miu-lab/midi_controller_2.0/src/app/MidiControllerApp.cpp

#include "MidiControllerApp.hpp"

#include "app/di/DependencyContainer.hpp"

#include "core/TaskScheduler.hpp"
#include "core/domain/interfaces/IConfiguration.hpp"
#include "core/domain/interfaces/IInputSystem.hpp"
#include "core/domain/interfaces/IMidiSystem.hpp"
#include "core/domain/interfaces/IUISystem.hpp"
#include "core/utils/Error.hpp"


MidiControllerApp::MidiControllerApp(std::shared_ptr<DependencyContainer> container)
    : m_container(container) {
    m_scheduler = m_container->resolve<TaskScheduler>();
}

MidiControllerApp::~MidiControllerApp() {
}

Result<bool> MidiControllerApp::init() {
    // 1. Obtention des références aux sous-systèmes
    m_configSystem = m_container->resolve<IConfiguration>();
    m_inputSystem = m_container->resolve<IInputSystem>();
    m_midiSystem = m_container->resolve<IMidiSystem>();
    m_uiSystem = m_container->resolve<IUISystem>();

    if (!m_configSystem || !m_inputSystem || !m_midiSystem || !m_uiSystem) {
        return Result<bool>::error({ErrorCode::DependencyMissing, "Sous-systèmes manquants"});
    }
    
    // Le décorateur MIDI pour les événements est maintenant créé et géré par MidiSubsystem

    return Result<bool>::success(true);
}

void MidiControllerApp::update() {
    // Mettre à jour le scheduler de tâches en premier
    if (m_scheduler) {
        m_scheduler->update();
    }
}
