miu-lab/midi_controller_2.0/src/app/MidiControllerApp.hpp

#pragma once

#include <memory>

#include "core/utils/Result.hpp"
#include "core/TaskScheduler.hpp"

// Déclarations anticipées
class DependencyContainer;
class IConfiguration;
class IInputSystem;
class IMidiSystem;
class IUISystem;

/**
 * @brief Application principale du contrôleur MIDI
 */
class MidiControllerApp {
public:
    explicit MidiControllerApp(std::shared_ptr<DependencyContainer> container);
    ~MidiControllerApp();

    // Méthodes principales
    Result<bool> init();
    void update();

private:
    // Conteneur de dépendances
    std::shared_ptr<DependencyContainer> m_container;

    // Sous-systèmes
    std::shared_ptr<IConfiguration> m_configSystem;
    std::shared_ptr<IInputSystem> m_inputSystem;
    std::shared_ptr<IMidiSystem> m_midiSystem;
    std::shared_ptr<IUISystem> m_uiSystem;
    
    std::shared_ptr<TaskScheduler> m_scheduler;
    
    
};
