miu-lab/midi_controller_2.0/src/adapters/secondary/hardware/input/encoders/EncoderManager.hpp

// adapters/secondary/hardware/input/encoders/EncoderManager.hpp
#pragma once
#include <memory>
#include <vector>

#include "adapters/secondary/hardware/input/encoders/EncoderConfig.hpp"
#include "adapters/secondary/hardware/input/encoders/QuadratureEncoder.hpp"
#include "core/ports/input/EncoderPort.hpp"

/**
 * @brief Construit et expose tous les EncoderPort* à partir de configs.
 */
class EncoderManager {
public:
    explicit EncoderManager(const std::vector<EncoderConfig>& cfgs);

    void updateAll();
    const std::vector<EncoderPort*>& getEncoders() const;

private:
    std::vector<std::unique_ptr<EncoderPort>> ownedEncoders_;
    std::vector<EncoderPort*> encoders_;
};
