miu-lab/midi_controller_2.0/src/core/use_cases/ButtonStateProcessor.hpp

#pragma once

#include <functional>
#include <vector>

/**
 * @brief Template pour traiter les changements d'état de boutons
 * 
 * Factorisation de la logique commune entre boutons normaux et boutons d'encodeurs.
 * Évite la duplication de code tout en gardant les performances optimales.
 */
template<typename Port>
void processButtonChanges(const std::vector<Port*>& ports, 
                         std::vector<bool>& lastStates,
                         std::function<void(uint16_t, bool)> callback) {
    for (size_t i = 0; i < ports.size(); ++i) {
        bool pressed = ports[i]->isPressed();
        if (pressed != lastStates[i]) {
            lastStates[i] = pressed;
            uint16_t buttonId = ports[i]->getId();
            callback(buttonId, pressed);
        }
    }
}
