miu-lab/midi_controller_2.0/src/adapters/secondary/midi/MidiMapper.cpp

#include "adapters/secondary/midi/MidiMapper.hpp"

#include <stdarg.h>

#include "config/SystemConstants.hpp"

#include "config/GlobalSettings.hpp"
  // Pour avoir accès à PERFORMANCE_MODE
#include "core/domain/events/core/EventTypes.hpp"
#include "tools/Diagnostics.hpp"

//=============================================================================
// Construction et initialisation
//=============================================================================

MidiMapper::MidiMapper(MidiOutputPort& midiOut, CommandManager& commandManager)
    : midiOut_(midiOut),
      commandManager_(commandManager),
      defaultConfig_(
          {0, 0, false})  // Canal 0, CC 0, mode absolu
{
    // Initialisation préalable des pool d'objets
    for (auto& cmd : midiCCCommandPool_) {
        cmd.reset(midiOut_, 0, 0, 0, 0);
    }

    for (auto& cmd : midiNoteCommandPool_) {
        cmd.reset(midiOut_, 0, 0, 0, 0);
    }
}

//=============================================================================
// Implémentation des méthodes utilitaires
//=============================================================================

uint32_t MidiMapper::makeCompositeKey(InputId controlId, MappingControlType type) {
    return static_cast<uint32_t>(controlId) << 8 | static_cast<uint8_t>(type);
}

SendMidiCCCommand& MidiMapper::getNextCCCommand() {
    SendMidiCCCommand& cmd = midiCCCommandPool_[nextCCCommandIndex_];
    nextCCCommandIndex_ = (nextCCCommandIndex_ + 1) % COMMAND_POOL_SIZE;
    return cmd;
}

SendMidiNoteCommand& MidiMapper::getNextNoteCommand() {
    SendMidiNoteCommand& cmd = midiNoteCommandPool_[nextNoteCommandIndex_];
    nextNoteCommandIndex_ = (nextNoteCommandIndex_ + 1) % COMMAND_POOL_SIZE;
    return cmd;
}

void MidiMapper::logDiagnostic(const char* format, ...) const {
#ifndef PERFORMANCE_MODE
    char buffer[100];
    va_list args;
    va_start(args, format);
    vsnprintf(buffer, sizeof(buffer), format, args);
    va_end(args);
    DIAG_ON_EVENT(buffer);
#endif
}


//=============================================================================
// Gestion des mappings
//=============================================================================

void MidiMapper::setMappingFromControlDefinition(const ControlDefinition& controlDef) {
    // Traiter le premier mapping MIDI trouvé dans la définition de contrôle
    for (const auto& mappingSpec : controlDef.mappings) {
        if (mappingSpec.role == MappingRole::MIDI) {
            // Extraire la configuration MIDI
            const auto& midiConfig = std::get<ControlDefinition::MidiConfig>(mappingSpec.config);
            
            // Créer une nouvelle info de mapping simplifiée
            MappingInfo info;
            info.midiConfig = midiConfig;
            info.lastMidiValue = 0;
            info.lastEncoderPosition = 0;  // Sera initialisé lors du premier appel
            info.isFirstCall = true;

            // Créer une clé composite qui inclut le type de contrôle
            uint32_t compositeKey = makeCompositeKey(controlDef.id, mappingSpec.appliesTo);

            // Supprimer l'ancien mapping s'il existe
            auto it = mappings_.find(compositeKey);
            if (it != mappings_.end()) {
                mappings_.erase(it);
            }

            // Ajouter le nouveau mapping
            mappings_[compositeKey] = std::move(info);

            // TODO DEBUG MSG

                          
            // Traiter seulement le premier mapping MIDI pour cette version
            break;
        }
    }
}

bool MidiMapper::removeMapping(InputId controlId) {
    // Nous devons vérifier tous les types de contrôle possibles
    bool removed = false;

    // Essayer de supprimer le mapping pour l'encodeur
    uint32_t encoderKey = makeCompositeKey(controlId, MappingControlType::ENCODER);
    auto encoderIt = mappings_.find(encoderKey);
    if (encoderIt != mappings_.end()) {
        mappings_.erase(encoderIt);
        removed = true;
    }

    // Essayer de supprimer le mapping pour le bouton d'encodeur
    uint32_t buttonKey = makeCompositeKey(controlId, MappingControlType::BUTTON);
    auto buttonIt = mappings_.find(buttonKey);
    if (buttonIt != mappings_.end()) {
        mappings_.erase(buttonIt);
        removed = true;
    }

    if (removed) {
        logDiagnostic("Mapping supprimé: ID=%d", controlId);
    }

    return removed;
}

bool MidiMapper::hasMapping(InputId controlId) const {
    // Vérifier tous les types de contrôle possibles
    uint32_t encoderKey = makeCompositeKey(controlId, MappingControlType::ENCODER);
    if (mappings_.find(encoderKey) != mappings_.end()) {
        return true;
    }

    uint32_t buttonKey = makeCompositeKey(controlId, MappingControlType::BUTTON);
    if (mappings_.find(buttonKey) != mappings_.end()) {
        return true;
    }

    return false;
}

ControlDefinition::MidiConfig MidiMapper::getMidiConfig(InputId controlId) const {
    // Vérifier pour encoder en premier
    uint32_t encoderKey = makeCompositeKey(controlId, MappingControlType::ENCODER);
    auto encoderIt = mappings_.find(encoderKey);
    if (encoderIt != mappings_.end()) {
        return encoderIt->second.midiConfig;
    }

    // Puis vérifier pour bouton d'encodeur
    uint32_t buttonKey = makeCompositeKey(controlId, MappingControlType::BUTTON);
    auto buttonIt = mappings_.find(buttonKey);
    if (buttonIt != mappings_.end()) {
        return buttonIt->second.midiConfig;
    }

    return defaultConfig_;
}


//=============================================================================
// Méthodes de traitement des encodeurs
//=============================================================================

bool MidiMapper::shouldProcessEncoder(EncoderId encoderId, int32_t position) {
    // TODO: Implémenter la limitation de taux et la détection de doublons
    // Pour l'instant, tous les événements sont traités
    return true;
}

int32_t MidiMapper::applyEncoderSensitivity(int32_t delta, EncoderId encoderId) {
    // Appliquer le facteur de sensibilité global
    float sensitivity = GlobalSettings::getInstance().getEncoderSensitivity();

    logDiagnostic("Pre-sensibilité: Enc=%d Delta=%ld", encoderId, delta);

    if (sensitivity != 1.0f) {
        // Appliquer la sensibilité tout en préservant le signe
        int32_t delta_sign = (delta > 0) ? 1 : -1;
        int32_t delta_abs = abs(delta);

        // Appliquer la sensibilité et assurer qu'un mouvement réel produit au moins 1 delta
        int32_t scaled_delta_abs = static_cast<int32_t>(delta_abs * sensitivity);
        if (scaled_delta_abs == 0 && delta_abs > 0) scaled_delta_abs = 1;

        // Reconstruire delta avec son signe
        int32_t new_delta = delta_sign * scaled_delta_abs;

        logDiagnostic("Post-sensibilité: Enc=%d Delta=%ld->%ld Sens=%.2f",
                      encoderId,
                      delta,
                      new_delta,
                      sensitivity);

        return new_delta;
    }

    return delta;
}

int16_t MidiMapper::calculateMidiValue(MappingInfo& info, int32_t delta, int32_t position) {
    const ControlDefinition::MidiConfig& midiConfig = info.midiConfig;
    
    uint8_t newValue;
    
    if (midiConfig.isRelative) {
        // Mode relatif : ajouter le delta à la dernière valeur
        int16_t temp = info.lastMidiValue + delta;
        newValue = constrain(temp, 0, 127);
    } else {
        // Mode absolu avec OFFSET : décaler la position pour que le centre soit 64
        // Plage encodeur typique : -127 à +127 -> MIDI 0 à 127
        int32_t offsetPosition = position + 64;  // Décaler de 64 pour centrer
        newValue = constrain(offsetPosition, 0, 127);
    }

    return newValue;
}

void MidiMapper::processEncoderChange(EncoderId encoderId, int32_t position) {
    // MidiMapper est responsable de tout le traitement des encodeurs MIDI,
    // y compris la limitation de taux, le suivi des positions et la détection des doublons.


    // Vérifier si l'encodeur doit être traité (limitation de taux)
    if (!shouldProcessEncoder(encoderId, position)) {
        return;
    }

    // Rechercher le mapping avec l'ID de l'encodeur et le type ENCODER_ROTATION
    uint32_t encoderKey = makeCompositeKey(encoderId, MappingControlType::ENCODER);
    auto it = mappings_.find(encoderKey);
    if (it == mappings_.end()) {
        return;  // Pas de mapping pour cet encodeur
    }

    auto& [key, mappingInfo] = *it;
    const ControlDefinition::MidiConfig& midiConfig = mappingInfo.midiConfig;

    // Si c'est le premier appel, initialiser avec la position actuelle
    if (mappingInfo.isFirstCall) {
        mappingInfo.lastEncoderPosition = position;
        mappingInfo.isFirstCall = false;
        return;  // Pas de changement lors de l'initialisation
    }

    // Calculer le delta de mouvement
    int32_t delta = position - mappingInfo.lastEncoderPosition;
    if (delta == 0) {
        return;  // Pas de changement
    }

    // Appliquer la sensibilité aux mouvements d'encodeur
    delta = applyEncoderSensitivity(delta, encoderId);

    // Mettre à jour la dernière position
    mappingInfo.lastEncoderPosition = position;

    // Calculer la nouvelle valeur MIDI selon le mode
    int16_t newValue = calculateMidiValue(mappingInfo, delta, position);

    // Ne rien faire si la valeur n'a pas changé
    if (newValue == mappingInfo.lastMidiValue) {
        return;
    }


    // Mettre à jour et envoyer la nouvelle valeur
    mappingInfo.lastMidiValue = static_cast<uint8_t>(newValue);

    // Utiliser le pool de commandes
    SendMidiCCCommand& command = getNextCCCommand();
    command.reset(midiOut_,
                  midiConfig.channel,
                  midiConfig.control,
                  static_cast<uint8_t>(newValue),
                  encoderId);
    commandManager_.executeShared(command);
}

//=============================================================================
// Méthodes de traitement des boutons
//=============================================================================

void MidiMapper::processButtonEvent(InputId buttonId, bool pressed, MappingControlType type) {

    // Créer une clé composite à partir de l'ID et du type
    uint32_t buttonKey = makeCompositeKey(buttonId, type);

    auto it = mappings_.find(buttonKey);
    if (it == mappings_.end()) {
        return;  // Pas de mapping pour ce bouton
    }

    MappingInfo& info = it->second;
    const ControlDefinition::MidiConfig& midiConfig = info.midiConfig;

    // Pour les boutons, on utilise des notes MIDI au lieu de CC
    uint8_t velocity = pressed ? 127 : 0;

    // Utiliser le pool d'objets pour créer la commande
    SendMidiNoteCommand& command = getNextNoteCommand();
    command.reset(midiOut_, midiConfig.channel, midiConfig.control, velocity);

    // Si c'est une note on, la stocker pour pouvoir la couper plus tard
    if (pressed) {
        // Pour les notes actives, nous gardons toujours des objets gérés par smart pointers
        // car elles doivent persister longtemps
        auto noteCmd = std::make_unique<SendMidiNoteCommand>(midiOut_,
                                                             midiConfig.channel,
                                                             midiConfig.control,
                                                             velocity);
        activeNotes_[buttonId] = std::move(noteCmd);
        activeNotes_[buttonId]->execute();
    } else {
        // Si c'est une note off, utiliser la commande et la supprimer
        auto noteIt = activeNotes_.find(buttonId);
        if (noteIt != activeNotes_.end()) {
            noteIt->second->undo();  // Undo = Note Off
            activeNotes_.erase(noteIt);
        } else {
            // Si pas de note active, simplement exécuter la commande du pool
            commandManager_.executeShared(command);
        }
    }
}


void MidiMapper::processButtonPress(ButtonId buttonId, bool pressed) {
    processButtonEvent(buttonId, pressed, MappingControlType::BUTTON);
}

//=============================================================================
// Méthodes de maintenance et mises à jour
//=============================================================================

void MidiMapper::update() {
    // Mettre à jour les commandes de notes actives
    for (auto& pair : activeNotes_) {
        pair.second->update();
    }

    // Supprimer les notes qui ne sont plus actives
    for (auto it = activeNotes_.begin(); it != activeNotes_.end();) {
        if (!it->second->isNoteActive()) {
            logDiagnostic("Note supprimée: ID=%d", it->first);
            it = activeNotes_.erase(it);
        } else {
            ++it;
        }
    }
}

//=============================================================================
// Gestion des événements
//=============================================================================

bool MidiMapper::onEvent(const Event& event) {
    // Traiter les différents types d'événements
    switch (event.getType()) {
    case EventTypes::HighPriorityEncoderChanged: {
        const HighPriorityEncoderChangedEvent& encEvent =
            static_cast<const HighPriorityEncoderChangedEvent&>(event);
        processEncoderChange(encEvent.encoderId, encEvent.position);
        return true;
    }


    case EventTypes::HighPriorityButtonPress: {
        const HighPriorityButtonPressEvent& buttonEvent =
            static_cast<const HighPriorityButtonPressEvent&>(event);
        // TODO DEBUG MSG
        processButtonPress(buttonEvent.buttonId, buttonEvent.pressed);
        return true;
    }

    // Gérer aussi les types standard d'événements pour la compatibilité
    case EventTypes::EncoderTurned: {
        const EncoderTurnedEvent& encEvent = static_cast<const EncoderTurnedEvent&>(event);
        processEncoderChange(encEvent.id, encEvent.position);
        return true;
    }

    case EventTypes::EncoderButton: {
        const EncoderButtonEvent& buttonEvent = static_cast<const EncoderButtonEvent&>(event);
        processButtonPress(buttonEvent.id, buttonEvent.pressed);
        return true;
    }

    case EventTypes::ButtonPressed: {
        const ButtonPressedEvent& buttonEvent = static_cast<const ButtonPressedEvent&>(event);
        processButtonPress(buttonEvent.id, true);
        return true;
    }

    case EventTypes::ButtonReleased: {
        const ButtonReleasedEvent& buttonEvent = static_cast<const ButtonReleasedEvent&>(event);
        processButtonPress(buttonEvent.id, false);
        return true;
    }
    }

    return false;  // Evénement non traité
}
