miu-lab/midi_controller_2.0/src/app/services/InputSystem.cpp

#include "app/services/InputSystem.hpp"

#include "app/di/DependencyContainer.hpp"
#include "app/services/NavigationConfigService.hpp"

InputSystem::InputSystem()
    : encoderManager_({}),
      processEncoders_(encoderManager_.getEncoders()),
      buttonManager_({}),
      processButtons_(buttonManager_.getButtons()),
      inputController_(nullptr),
      container_(nullptr),
      usingContainer_(false) {
      
    // Créer un service de navigation par défaut
    auto navConfigService = std::make_shared<NavigationConfigService>();
    
    // Créer InputController
    inputController_ = std::make_shared<InputController>(navConfigService);

    // Configurer les processeurs
    processEncoders_.setInputController(inputController_.get());
    processButtons_.setInputController(inputController_.get());
}

InputSystem::InputSystem(std::shared_ptr<DependencyContainer> container)
    : encoderManager_({}),
      processEncoders_(encoderManager_.getEncoders()),
      buttonManager_({}),
      processButtons_(buttonManager_.getButtons()),
      inputController_(nullptr),
      container_(container),
      usingContainer_(true) {
      
    initializeDependencies();
}

void InputSystem::initializeDependencies() {
#ifndef DISABLE_CONTROLLERS
    // Récupérer NavigationConfigService
    std::shared_ptr<NavigationConfigService> navConfigService;
    
    if (usingContainer_ && container_) {
        // Essayer de récupérer depuis le container
        navConfigService = container_->resolve<NavigationConfigService>();
        
        // Si le service n'est pas dans le container, créer une nouvelle instance
        if (!navConfigService) {
            navConfigService = std::make_shared<NavigationConfigService>();
            container_->registerDependency<NavigationConfigService>(navConfigService);
        }
    } else {
        // Créer un service de navigation par défaut
        navConfigService = std::make_shared<NavigationConfigService>();
    }
    
    // Créer InputController
    inputController_ = std::make_shared<InputController>(navConfigService);

    if (usingContainer_ && container_) {
        // Enregistrer dans le container
        container_->registerDependency<InputController>(inputController_);
    }

    // Configurer les processeurs
    processEncoders_.setInputController(inputController_.get());
    processButtons_.setInputController(inputController_.get());
#endif
}

void InputSystem::init() {
    // Initialiser l'état initial des encodeurs et boutons
    encoderManager_.updateAll();
    buttonManager_.updateAll();
    processButtons_.initStates();  // Initialiser les états sans déclencher d'événements

#ifndef DISABLE_CONTROLLERS
    // Configurer le contrôleur d'entrée avec les callbacks par défaut
    // Ces callbacks utilisent le nouveau système d'événements
    inputController_->setNavigationEncoderCallback(
        [](EncoderId id, int32_t absPos, int8_t relChange) {
            // Publier l'événement pour les encodeurs de navigation dans le nouveau système
            EncoderTurnedEvent event(id, absPos, relChange);
            EventBus::getInstance().publish(event);
        });

    inputController_->setMidiEncoderCallback([](EncoderId id, int32_t absPos, int8_t relChange) {
        // Publier l'événement pour les encodeurs MIDI dans le nouveau système
        // MidiMapper se chargera de gérer les cas où absPos est hors limites (0-127)
        // et de détecter les changements de direction
        EncoderTurnedEvent event(id, absPos, relChange);
        EventBus::getInstance().publish(event);
    });

    // Callbacks pour les boutons d'encodeurs (navigation et MIDI)
    auto encoderButtonCallback = [](EncoderId id, bool pressed) {
        EncoderButtonEvent event(id, pressed);
        EventBus::getInstance().publish(event);
    };
    inputController_->setNavigationEncoderButtonCallback(encoderButtonCallback);
    inputController_->setMidiEncoderButtonCallback(encoderButtonCallback);

    // Callbacks pour les boutons (navigation et MIDI)
    auto buttonCallback = [](ButtonId id, bool pressed) {
        if (pressed) {
            ButtonPressedEvent event(id);
            EventBus::getInstance().publish(event);
        } else {
            ButtonReleasedEvent event(id);
            EventBus::getInstance().publish(event);
        }
    };
    inputController_->setNavigationButtonCallback(buttonCallback);
    inputController_->setMidiButtonCallback(buttonCallback);
#endif
}

void InputSystem::init(const std::vector<EncoderConfig>& encoderConfigs,
                       const std::vector<ButtonConfig>& buttonConfigs) {
    // Reconfigurer les gestionnaires
    encoderManager_ = EncoderManager(encoderConfigs);
    processEncoders_ = ProcessEncoders(encoderManager_.getEncoders());
    buttonManager_ = DigitalButtonManager(buttonConfigs);
    processButtons_ = ProcessButtons(buttonManager_.getButtons());

#ifndef DISABLE_CONTROLLERS
    // Reconfigurer les processeurs pour utiliser l'InputController
    processEncoders_.setInputController(inputController_.get());
    processButtons_.setInputController(inputController_.get());
#endif

    // Initialiser l'état initial
    init();
}

InputController& InputSystem::getInputController() {
#ifndef DISABLE_CONTROLLERS
    return *inputController_;
#else
    // En mode DISABLE_CONTROLLERS, créer un contrôleur temporaire
    static auto navConfigService = std::make_shared<NavigationConfigService>();
    static InputController nullController(navConfigService);
    return nullController;
#endif
}

void InputSystem::update() {
    // Lecture et publication des mouvements d'encodeurs
    encoderManager_.updateAll();
    processEncoders_.update();

    // Lecture et publication des états de boutons
    buttonManager_.updateAll();
    processButtons_.update();
}
