miu-lab/midi_controller_2.0/src/app/services/MidiSystem.cpp

#include "app/services/MidiSystem.hpp"

#include "app/services/MidiSystemListener.hpp"
#include "config/debug/DebugMacros.hpp"
#include "core/domain/events/EventSystem.hpp"
#include "core/domain/strategies/MidiMappingFactory.hpp"
#include "tools/Diagnostics.hpp"

MidiSystem::MidiSystem(ProfileManager& profileManager)
    : rawMidiOut_(),
      bufferedMidiOut_(rawMidiOut_),
      midiInHandler_(),
      commandManager_(),
      midiMapper_(bufferedMidiOut_, commandManager_),
      profileManager_(profileManager),
      simpleListener_(nullptr),
      eventListener_(nullptr),
      simpleListenerSubId_(0),
      eventListenerSubId_(0) {
    // Note: InputRouter n'est plus utilisé directement, on utilise MidiMapper à la place
    DIAG_ON_EVENT("MidiSystem: Constructeur appelé");
}

MidiSystem::~MidiSystem() {
    DIAG_ON_EVENT("MidiSystem: Destructeur appelé");

    // Se désabonner du bus d'événements
    auto& eventBus = EventBus::getInstance();

    if (simpleListenerSubId_ != 0) {
        eventBus.unsubscribe(simpleListenerSubId_);
    }

    if (eventListenerSubId_ != 0) {
        eventBus.unsubscribe(eventListenerSubId_);
    }

    // Les écouteurs seront automatiquement libérés par les destructeurs des smart pointers
}

void MidiSystem::init() {
#if defined(DEBUG) && defined(DEBUG_MIDI_SYSTEM)
    Serial.println(F("MidiSystem::init() called"));
#endif
    DIAG_ON_EVENT("MidiSystem: Initialisation simple");

    initSubscriptions();

    // Initialiser les mappings à partir du ProfileManager
    for (const auto& mapping : profileManager_.getAllMappings()) {
        // Par défaut, utiliser une stratégie absolue pour les encodeurs
        // et une stratégie relative pour les boutons
        bool isRelative = mapping.midiControl.relative;

        std::unique_ptr<IMidiMappingStrategy> strategy;
        if (isRelative) {
            strategy = MidiMappingFactory::createRelative();
        } else {
            strategy = MidiMappingFactory::createAbsolute(0, 127);
        }

        midiMapper_.setMapping(mapping.controlId, mapping.midiControl, std::move(strategy));
    }
}

void MidiSystem::init(NavigationConfigService& navService) {
#if defined(DEBUG) && defined(DEBUG_MIDI_SYSTEM)
    Serial.println(F("MidiSystem::init(NavigationConfigService&) called"));
#endif
    DIAG_ON_EVENT("MidiSystem: Initialisation avec navigation");

    // D'abord se désabonner de tout écouteur existant, y compris le simpleListener
    auto& eventBus = EventBus::getInstance();

    // Désabonner l'écouteur simple et le réinitialiser (à nullptr)
    if (simpleListener_) {
        if (simpleListenerSubId_ != 0) {
            eventBus.unsubscribe(simpleListenerSubId_);
            simpleListenerSubId_ = 0;
        }
        simpleListener_.reset();
    }

    // Désabonner l'écouteur existant avec navigation et le réinitialiser
    if (eventListener_) {
        if (eventListenerSubId_ != 0) {
            eventBus.unsubscribe(eventListenerSubId_);
            eventListenerSubId_ = 0;
        }
        eventListener_.reset();
    }

    // Initialiser les mappings comme dans init() mais sans créer un simple listener
    int mappingCount = 0;
    for (const auto& mapping : profileManager_.getAllMappings()) {
        bool isRelative = mapping.midiControl.relative;

        std::unique_ptr<IMidiMappingStrategy> strategy;
        if (isRelative) {
            strategy = MidiMappingFactory::createRelative();
        } else {
            strategy = MidiMappingFactory::createAbsolute(0, 127);
        }

        midiMapper_.setMapping(mapping.controlId, mapping.midiControl, std::move(strategy));
        mappingCount++;
    }

    // Diagnostic du nombre de mappings
    char mappingEvent[50];
    snprintf(mappingEvent,
             sizeof(mappingEvent),
             "MidiSystem: %d mappings configurés",
             mappingCount);
    DIAG_ON_EVENT(mappingEvent);

    // Créer uniquement l'écouteur avec navigation
    eventListener_ = std::make_unique<MidiSystemEventListener>(*this, navService);

    // S'abonner au bus d'événements avec l'objet et enregistrer l'ID
    eventListenerSubId_ = eventBus.subscribe(eventListener_.get());

    // Diagnostic de l'abonnement
    char subscriptionEvent[50];
    snprintf(subscriptionEvent,
             sizeof(subscriptionEvent),
             "MidiSystem: Abonnement ID=%d (avec navigation)",
             eventListenerSubId_);
    DIAG_ON_EVENT(subscriptionEvent);
}

void MidiSystem::update() {
    // Traiter les messages MIDI entrants
    midiInHandler_.update();

    // Mettre à jour le mapper MIDI (pour les commandes temporisées)
    midiMapper_.update();

    // Envoyer les messages en attente dans le buffer
    bufferedMidiOut_.update();
}

IMidiOut& MidiSystem::getMidiOut() {
    return bufferedMidiOut_;
}

CommandManager& MidiSystem::getCommandManager() {
    return commandManager_;
}

MidiMapper& MidiSystem::getMidiMapper() {
    return midiMapper_;
}

void MidiSystem::initSubscriptions() {
#if defined(DEBUG) && defined(DEBUG_MIDI_SYSTEM)
    Serial.println(F("MidiSystem::initSubscriptions() called"));
#endif
    DIAG_ON_EVENT("MidiSystem: Initialisation des abonnements");

    // Libérer l'écouteur existant s'il y en a un
    if (simpleListener_) {
        auto& eventBus = EventBus::getInstance();
        if (simpleListenerSubId_ != 0) {
            eventBus.unsubscribe(simpleListenerSubId_);
        }
        simpleListener_.reset();
    }

    // Créer une instance de l'écouteur
    simpleListener_ = std::make_unique<MidiSystemSimpleListener>(*this);

    // S'abonner au bus d'événements et enregistrer l'ID d'abonnement
    auto& eventBus = EventBus::getInstance();
    simpleListenerSubId_ = eventBus.subscribe(simpleListener_.get());

    // Diagnostic de l'abonnement
    char subscriptionEvent[50];
    snprintf(subscriptionEvent,
             sizeof(subscriptionEvent),
             "MidiSystem: Abonnement ID=%d (simple)",
             simpleListenerSubId_);
    DIAG_ON_EVENT(subscriptionEvent);
}
