miu-lab/midi_controller_2.0/src/name.c

#include "usb_names.h"

// Nom du périphérique USB MIDI

#define MIDI_NAME   {'P','C','-','M','I','D','I',' ','S','t','u','d','i','o'}
#define MIDI_NAME_LEN  14

// Do not change this part.  This exact format is required by USB.
struct usb_string_descriptor_struct usb_string_product_name = {
        2 + MIDI_NAME_LEN * 2,
        3,
        MIDI_NAME
};
