miu-lab/midi_controller_2.0/src/adapters/secondary/hardware/display/DisplayManagerAdapter.cpp

#include "DisplayManagerAdapter.hpp"
#include <Arduino.h>
#include "config/SystemConstants.hpp"

DisplayManagerAdapter::DisplayManagerAdapter(std::shared_ptr<Ili9341LvglBridge> lvglBridge)
    : lvglBridge_(lvglBridge)
    , refreshIntervalMs_(SystemConstants::Performance::DISPLAY_REFRESH_PERIOD_MS * SystemConstants::Performance::VSYNC_SPACING)
    , lastRefreshTime_(0) {
}

void DisplayManagerAdapter::update() {
    if (!lvglBridge_) {
        return;
    }
    
    unsigned long currentTime = getCurrentTime();
    
    if ((currentTime - lastRefreshTime_) >= refreshIntervalMs_) {
        lvglBridge_->refreshDisplay();
        lastRefreshTime_ = currentTime;
    }
}

void DisplayManagerAdapter::forceRefresh() {
    if (!lvglBridge_) {
        return;
    }
    
    lvglBridge_->refreshDisplay();
    lastRefreshTime_ = getCurrentTime();
}

void DisplayManagerAdapter::setRefreshInterval(unsigned long intervalMs) {
    refreshIntervalMs_ = intervalMs;
}

unsigned long DisplayManagerAdapter::getRefreshInterval() const {
    return refreshIntervalMs_;
}

unsigned long DisplayManagerAdapter::getCurrentTime() const {
    return millis();
}
