miu-lab/midi_controller_2.0/src/core/use_cases/ProcessButtons.hpp

#pragma once
#include <functional>
#include <vector>

#include "config/common/CommonIncludes.hpp"
#include "core/controllers/InputController.hpp"
#include "core/ports/input/ButtonPort.hpp"

class ProcessButtons {
public:
    /**
     * @brief Constructeur
     * @param buttons Liste des boutons à traiter
     */
    explicit ProcessButtons(const std::vector<ButtonPort*>& buttons);

    /**
     * @brief Type de callback pour les événements de bouton
     */
    using ButtonStateChangedCallback = std::function<void(uint8_t, bool)>;

    /**
     * @brief Définit le callback pour les changements d'état des boutons
     * @param callback Fonction à appeler
     */
    void setOnButtonStateChangedCallback(ButtonStateChangedCallback callback);

    /**
     * @brief Définit le contrôleur d'entrée à utiliser
     * @param inputController Contrôleur d'entrée
     */
    void setInputController(InputController* inputController);

    /**
     * @brief Mise à jour des boutons
     */
    void update();

    /**
     * @brief Initialise les états sans déclencher d'événements
     */
    void initStates();

private:
    std::vector<ButtonPort*> buttons_;
    std::vector<bool> lastPressed_;
    bool initialized_;
    ButtonStateChangedCallback onButtonStateChangedCallback_;
    InputController* inputController_;
    bool useInputController_;
};
