miu-lab/midi_controller_2.0/src/app/services/InputSystem.hpp

#pragma once
#include <vector>
#include <memory>

// Forward declarations
class DependencyContainer;
class NavigationConfigService;

#include "adapters/secondary/hardware/buttons/DigitalButtonManager.hpp"
#include "adapters/secondary/hardware/encoders/EncoderManager.hpp"
#include "core/controllers/InputController.hpp"
#include "core/controllers/UIController.hpp"
#include "core/domain/events/EventSystem.hpp"
#include "core/use_cases/ProcessButtons.hpp"
#include "core/use_cases/ProcessEncoders.hpp"

/**
 * @brief Système gérant toutes les entrées physiques
 *
 * Ce système regroupe les gestionnaires d'encodeurs et de boutons,
 * ainsi que le traitement des entrées en événements.
 */
class InputSystem {
public:
    /**
     * @brief Construit un nouveau système d'entrée (original)
     */
    InputSystem();
    
    /**
     * @brief Construit un nouveau système d'entrée avec injection de dépendances
     * @param container Conteneur de dépendances
     */
    explicit InputSystem(std::shared_ptr<DependencyContainer> container);

    /**
     * @brief Initialise le système d'entrée
     */
    void init();

    /**
     * @brief Initialise le système d'entrée avec les configurations spécifiées
     * @param encoderConfigs Configuration des encodeurs
     * @param buttonConfigs Configuration des boutons
     */
    void init(const std::vector<EncoderConfig>& encoderConfigs,
              const std::vector<ButtonConfig>& buttonConfigs);

    /**
     * @brief Met à jour le système d'entrée
     *
     * Lit les états des encodeurs et des boutons et génère les événements correspondants.
     */
    void update();

    /**
     * @brief Obtient le contrôleur d'entrée
     * @return Référence au contrôleur d'entrée
     */
    InputController& getInputController();

private:
    EncoderManager encoderManager_;       // Gestionnaire des encodeurs
    ProcessEncoders processEncoders_;     // Traitement des encodeurs
    DigitalButtonManager buttonManager_;  // Gestionnaire des boutons
    ProcessButtons processButtons_;       // Traitement des boutons
    std::shared_ptr<InputController> inputController_;    // Contrôleur d'entrée
    
    // Conteneur de dépendances (peut être nullptr pour l'ancien constructeur)
    std::shared_ptr<DependencyContainer> container_;
    
    // Flag pour savoir si on utilise le container
    bool usingContainer_ = false;
    
    /**
     * @brief Initialise les dépendances internes
     */
    void initializeDependencies();
};
