miu-lab/midi_controller_2.0/src/app/services/ConfigurationService.hpp

#pragma once
#include <memory>
#include <vector>

#include "adapters/secondary/hardware/buttons/DigitalButtonConfig.hpp"
#include "adapters/secondary/hardware/encoders/EncoderConfig.hpp"
#include "adapters/secondary/storage/ProfileManager.hpp"
#include "app/services/NavigationConfigService.hpp"
#include "config/ApplicationConfiguration.hpp"
#include "core/domain/types.hpp"

/**
 * @brief Service centralisant la gestion des configurations
 *
 * Ce service est responsable du chargement et de la gestion de toutes
 * les configurations de l'application : encodeurs, boutons, mappings MIDI,
 * contrôles de navigation, etc.
 */
class ConfigurationService {
public:
    /**
     * @brief Construit un nouveau service de configuration
     * @param appConfig Configuration de l'application
     */
    ConfigurationService(const ApplicationConfiguration& appConfig);

    /**
     * @brief Applique les configurations aux différents services
     * @param profileManager Gestionnaire de profils pour les mappings MIDI
     * @param navService Service de configuration pour la navigation
     */
    void applyConfigurations(ProfileManager& profileManager, NavigationConfigService& navService);

    /**
     * @brief Accès à la configuration des encodeurs
     * @return Référence constante au vecteur de configurations d'encodeurs
     */
    const std::vector<EncoderConfig>& encoderConfigs() const;

    /**
     * @brief Accès à la configuration des boutons
     * @return Référence constante au vecteur de configurations de boutons
     */
    const std::vector<ButtonConfig>& buttonConfigs() const;

private:
    // Référence à la configuration de l'application
    const ApplicationConfiguration& appConfig_;
};
