miu-lab/midi_controller_2.0/src/app/InitializationScript.hpp

#pragma once

#include <memory>

#include "app/di/DependencyContainer.hpp"
#include "config/ApplicationConfiguration.hpp"
#include "core/utils/Result.hpp"

// Déclarations anticipées pour réduire les inclusions
class NavigationConfigService;
class NavigationStateManager;
class NavigationController;
class NavigationSubsystem;
class CommandManager;
class InputController;
class InputSubsystem;
class MidiSubsystem;
class UISubsystem;
class MenuController;

/**
 * @brief Script d'initialisation du système
 */
class InitializationScript {
public:
    /**
     * @brief Initialise le conteneur de dépendances avec tous les composants requis
     */
    static Result<bool> initializeContainer(
        std::shared_ptr<DependencyContainer> container, const ApplicationConfiguration& config);

private:
    // Structure de données pour les initialisations des sous-systèmes
    struct SubsystemInfo {
        const char* name;
        std::shared_ptr<void> instance;
        std::function<Result<bool>()> initFn;
    };

    // Étapes d'initialisation ordonnées
    static void registerBaseServices(std::shared_ptr<DependencyContainer> container,
                                     const ApplicationConfiguration& config);

    static Result<bool> setupHardwareAdapters(
        std::shared_ptr<DependencyContainer> container);

    static Result<bool> initializeSubsystems(
        std::shared_ptr<DependencyContainer> container);

    static bool setupControllers(std::shared_ptr<DependencyContainer> container);
    
    static void registerNavigationServices(std::shared_ptr<DependencyContainer> container);

    // Configuration des écouteurs MIDI prioritaires
    static void setupMidiEventListeners(std::shared_ptr<DependencyContainer> container);
    
    // Création du contrôleur d'entrée après l'initialisation des sous-systèmes
    static Result<bool> createInputController(std::shared_ptr<DependencyContainer> container);
    
    // REFACTOR: Méthode supprimée - synchronisation automatique maintenant

private:
};
